Solomute/STEVEannouncer/Spice/Talkback.asc

B1: bv; V=v(o1,o2)
C1: cap; 22µ
C2: cap; 22µ
C3: cap; 100n
C4: cap; 100n
R1: res; 20k
R2: res; 20k
R3: res; 1k
R4: res; 1k
R5: res; 100
R6: res; 1k
R7: res; 20k
R8: res; 20k
R9: res; 1k
R10: res; 1k
R11: res; 100
R12: res; 1k
U2: UniversalOpAmp5
U3: UniversalOpAmp5
V1: voltage; 5
V2: voltage; 5
V3: voltage; SINE(0 1 1k); AC 1
Named nets: 0, -5, +5, out+, out-, o1, o2, out
.tran 10m
.lib opamp.sub
.ac oct 10 20 20k
.model MYSW SW(Ron=1 Roff=1Meg Vt=.5)
