Solomute/STEVEannouncer/Spice/Buttons.asc

C1: cap; 100n
C2: cap; 100n
D1: schottky; BAT54
R1: res; 330k
R2: res; 4Meg
R3: res; 20k
R4: res; 330k
R5: res; 4Meg
R7: res; 20k
S1: sw; Myswitch
S2: sw; Myswitch
V1: voltage; 5
V2: voltage; PULSE(0 1 250m 1p 1p 250m 500m)
V3: voltage; 5
V4: voltage; PULSE(0 1 125m 1p 1p 125m 250m)
V5: voltage; .8
V6: voltage; 1.4
Named nets: 0, tblogic, mutelogic, tb, mute, logiclow, logichigh
.model MySwitch SW(Ron=1m Roff=1Gig Vt=.5)
.tran 1
