Solomute/STEVEannouncer/Spice/MIcpre.asc

C1: cap; 22µ
C2: cap; 22µ
C3: cap; 100µ
C4: cap; 10µ
R1: res; 1k
R2: res; 1k
R3: res; 20k
R4: res; 270
R6: res; 10k
R7: res; 10k
U2: THAT1512
U3: opamp
V1: voltage; 0; AC 1
V2: voltage; 5
V3: voltage; 5
Named nets: 0, out
.tran 10m
.ac oct 10 1 1gig
.lib opamp.sub
.noise v(out) V1 oct 10 1 1gig
