Solomute/STEVEannouncer/Spice/Power.asc

C1: cap; 1000µ
C2: cap; 1µ
D1: zener; STZ5_6N
D2: schottky; 1N5819
D3: schottky; 1N5819
I1: load; 20m; AC 1
Q1: npn; 2N3904
Q2: npn; 2N3904
Q3: npn; 2N3904
R1: res; 10
R2: res; 1Meg
R3: res; 330k
R4: res; 1
R5: res; 20k
V1: voltage; 30; AC 1
V2: voltage; 12
Named nets: 0, out, in
.tran 1 startup
.lib opamp.sub
.ac oct 10 1m 20k
.step oct param R .1 100 3
.four 1k v(in)
