Solomute/STEVEannouncer/Spice/VCA.asc

C1: cap; 100p
C2: cap; 100p
C3: cap; 1µ
R1: res; 20k
R2: res; 6.8k
R3: res; 6.8k
U2: opamp
U4: THAT2162
V1: voltage; 5
V2: voltage; -5; AC 0
V3: voltage; PULSE(-15 15 0 1p 1p .5m 1m); AC 1
Named nets: 0, -5v, +5v, out
.tran 0 10m 0 1u
.lib opamp.sub
.ac oct 10 1 20k
.four 1k v(out)
